ElectronicCats/meteoritoboard/Firmware/meteorito/configuracion.h

/*
 * Archivo de configuracion de claves WiFi, Token y servidor
 */
const char* ssid = "NombreDeTuWiFi";
const char* password = "ContraseñaDeTuWiFi";

//Pagina de conexión con el servidor
const char* Servidor  = "redmet.org";

//Token de acceso a redmet.org
const String Token = "TokenUnicoParaRedMet";
